userx14/AG-IUP32-8/schematic/HVboard.kicad_sch

## KiCad design schematic/HVboard.kicad_sch (2025-08-31)

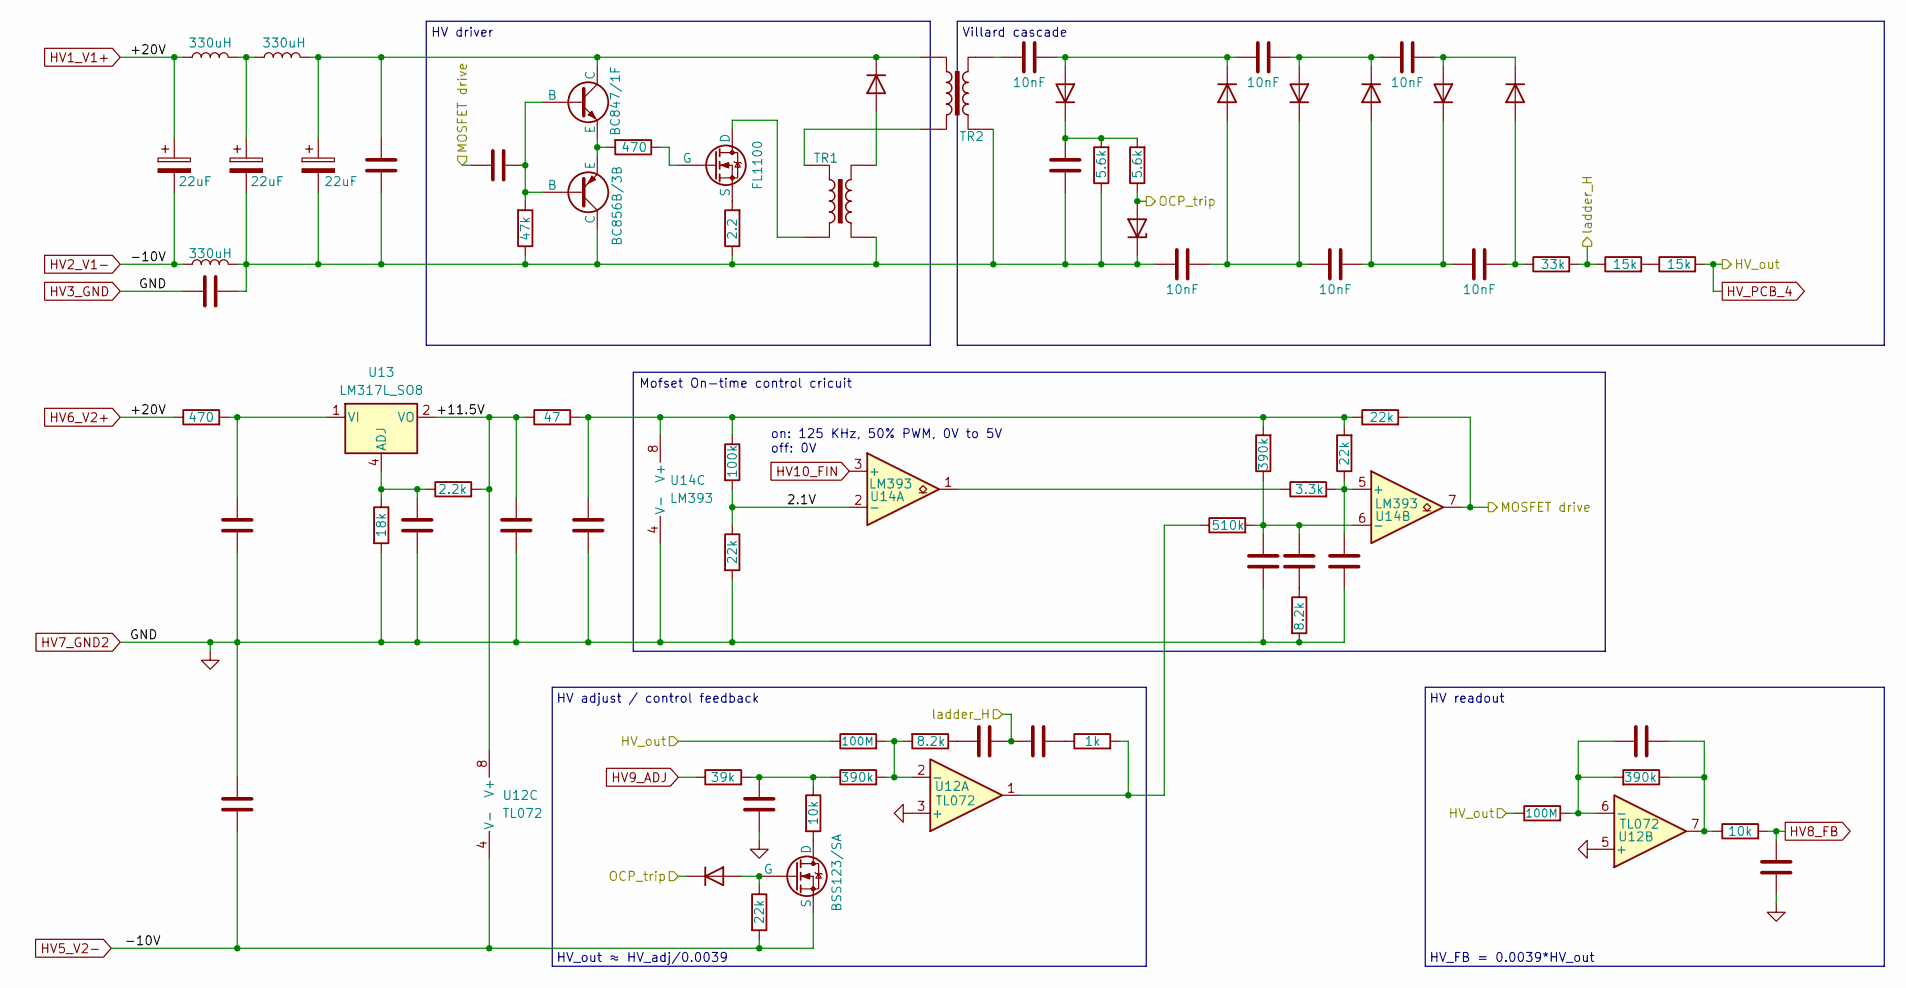
[picture p2: schematic HVboard.kicad_sch]

Parts:
C13, C29, C30, C33, C34, C35, C39: 10nF
C36, C37, C40, C41, C42, C43, C44, C46, C47, C48, C50, C55, C56, C57: C
C38, C53: (no value)
C51, C52, C54: 22uF
D16, D17, D18, D19, D20, D21, D22, D24: D
D25: D_Zener
L5, L6, L7: 330uH
Q1: FL1100
Q10: BSS123/SA
Q14: BC847/1F
Q16: BC856B/3B
R70, R71: 15k
R72: 33k
R73, R85: 8.2k
R74: 1k
R75, R94: 470
R76: 18k
R77: 2.2k
R78: 47
R79, R81, R83, R90: 22k
R80, R88, R98: 390k
R82: 100k
R84: 3.3k
R86: 510k
R87: 39k
R89, R99: 10k
R91, R97: 100M
R92, R96: 5.6k
R93: 2.2
R95: 47k
TR1: TRANSF1
TR2: TRANSF2
U12: TL072
U13: LM317L_SO8; SOIC-8_3.9x4.9mm_P1.27mm
U14: LM393

Connections:
2.1V: R82.2, R83.1, U14.2 (-)
+11.5V: C42.2, R77.2, R78.1, U12.8 (V+), U13.2 (VO), U13.3 (VO), U13.6 (VO), U13.7 (VO)
GND: C38.1, C40.1, C41.1, C42.1, C43.1, C44.1, C47.1, C48.2, C53.1, C57.1, R76.2, R83.2, R85.2, U12.3 (+), U12.5 (+), U14.4 (V-)
HV1_V1+: C54.1, L5.1, R75.1
HV2_V1-: C38.2, C54.2, L6.1, Q10.3 (S), R90.2, U12.4 (V-)
HV8_FB: C57.2, R99.2
HV9_ADJ: R87.1
HV10_FIN: U14.3 (+)
HV_PCB_4: R70.2, R91.1, R97.1
MOSFET drive: C55.2, R79.2, U14.7
unnamed: C13.1, C33.2, D17.1 (K), D18.2 (A)
unnamed: C13.2, D16.2 (A), R72.1
unnamed: C29.1, C30.2, D18.1 (K), D19.2 (A)
unnamed: C29.2, D16.1 (K), D17.2 (A)
unnamed: C30.1, C39.2, D20.1 (K), D22.2 (A)
unnamed: C33.1, C34.2, D19.1 (K), D20.2 (A)
unnamed: C34.1, C35.2, C51.2, C52.2, C53.2, C56.2, D25.1 (K), L6.2, Q16.1 (C), R93.1, R95.1, R96.1, TR1.1, TR2.3
unnamed: C35.1, D22.1 (K), R92.2, R96.2
unnamed: C36.1, R73.1
unnamed: C37.1, R74.1
unnamed: C39.1, TR2.4
unnamed: C40.2, R75.2, U13.1 (VI)
unnamed: C41.2, R76.1, R77.1, U13.4 (ADJ)
unnamed: C43.2, R78.2, R79.1, R80.2, R81.2, R82.1, U14.8 (V+)
unnamed: C44.2, R81.1, R84.2, U14.5 (+)
unnamed: C46.1, R85.1
unnamed: C46.2, C47.2, R80.1, R86.2, U14.6 (-)
unnamed: C48.1, R87.2, R88.1, R89.1
unnamed: C50.1, R97.2, R98.2, U12.6 (-)
unnamed: C50.2, R98.1, R99.1, U12.7
unnamed: C51.1, L5.2, L7.1
unnamed: C52.1, C56.1, D24.1 (K), L7.2, Q14.1 (C), TR2.1
unnamed: C55.1, Q14.2 (B), Q16.2 (B), R95.2
unnamed: D21.2 (A), Q10.2 (G), R90.1
unnamed: D24.2 (A), TR1.2
unnamed: Q1.1 (D), TR1.4
unnamed: Q1.2 (G), R94.1
unnamed: Q1.3 (S), R93.2
unnamed: Q10.1 (D), R89.2
unnamed: Q14.3 (E), Q16.3 (E), R94.2
unnamed: R70.1, R71.2
unnamed: R73.2, R88.2, R91.2, U12.2 (-)
unnamed: R74.2, R86.1, U12.1
unnamed: R84.1, U14.1
unnamed: TR1.3, TR2.2
OCP_trip: D21.1 (K), D25.2 (A), R92.1
ladder_H: C36.2, C37.2, R71.1, R72.2

Notes on the sheet:
HV_FB = 0.0039*HV_out
HV readout
Villard cascade
on: 125 KHz, 50% PWM, 0V to 5V off: 0V
HV driver
HV_out ≈ HV_adj/0.0039
Mofset On-time control cricuit
HV adjust / control feedback
