userx14/AG-IUP32-8/schematic/schematic.kicad_sch

## KiCad design schematic/schematic.kicad_sch (2025-08-31)

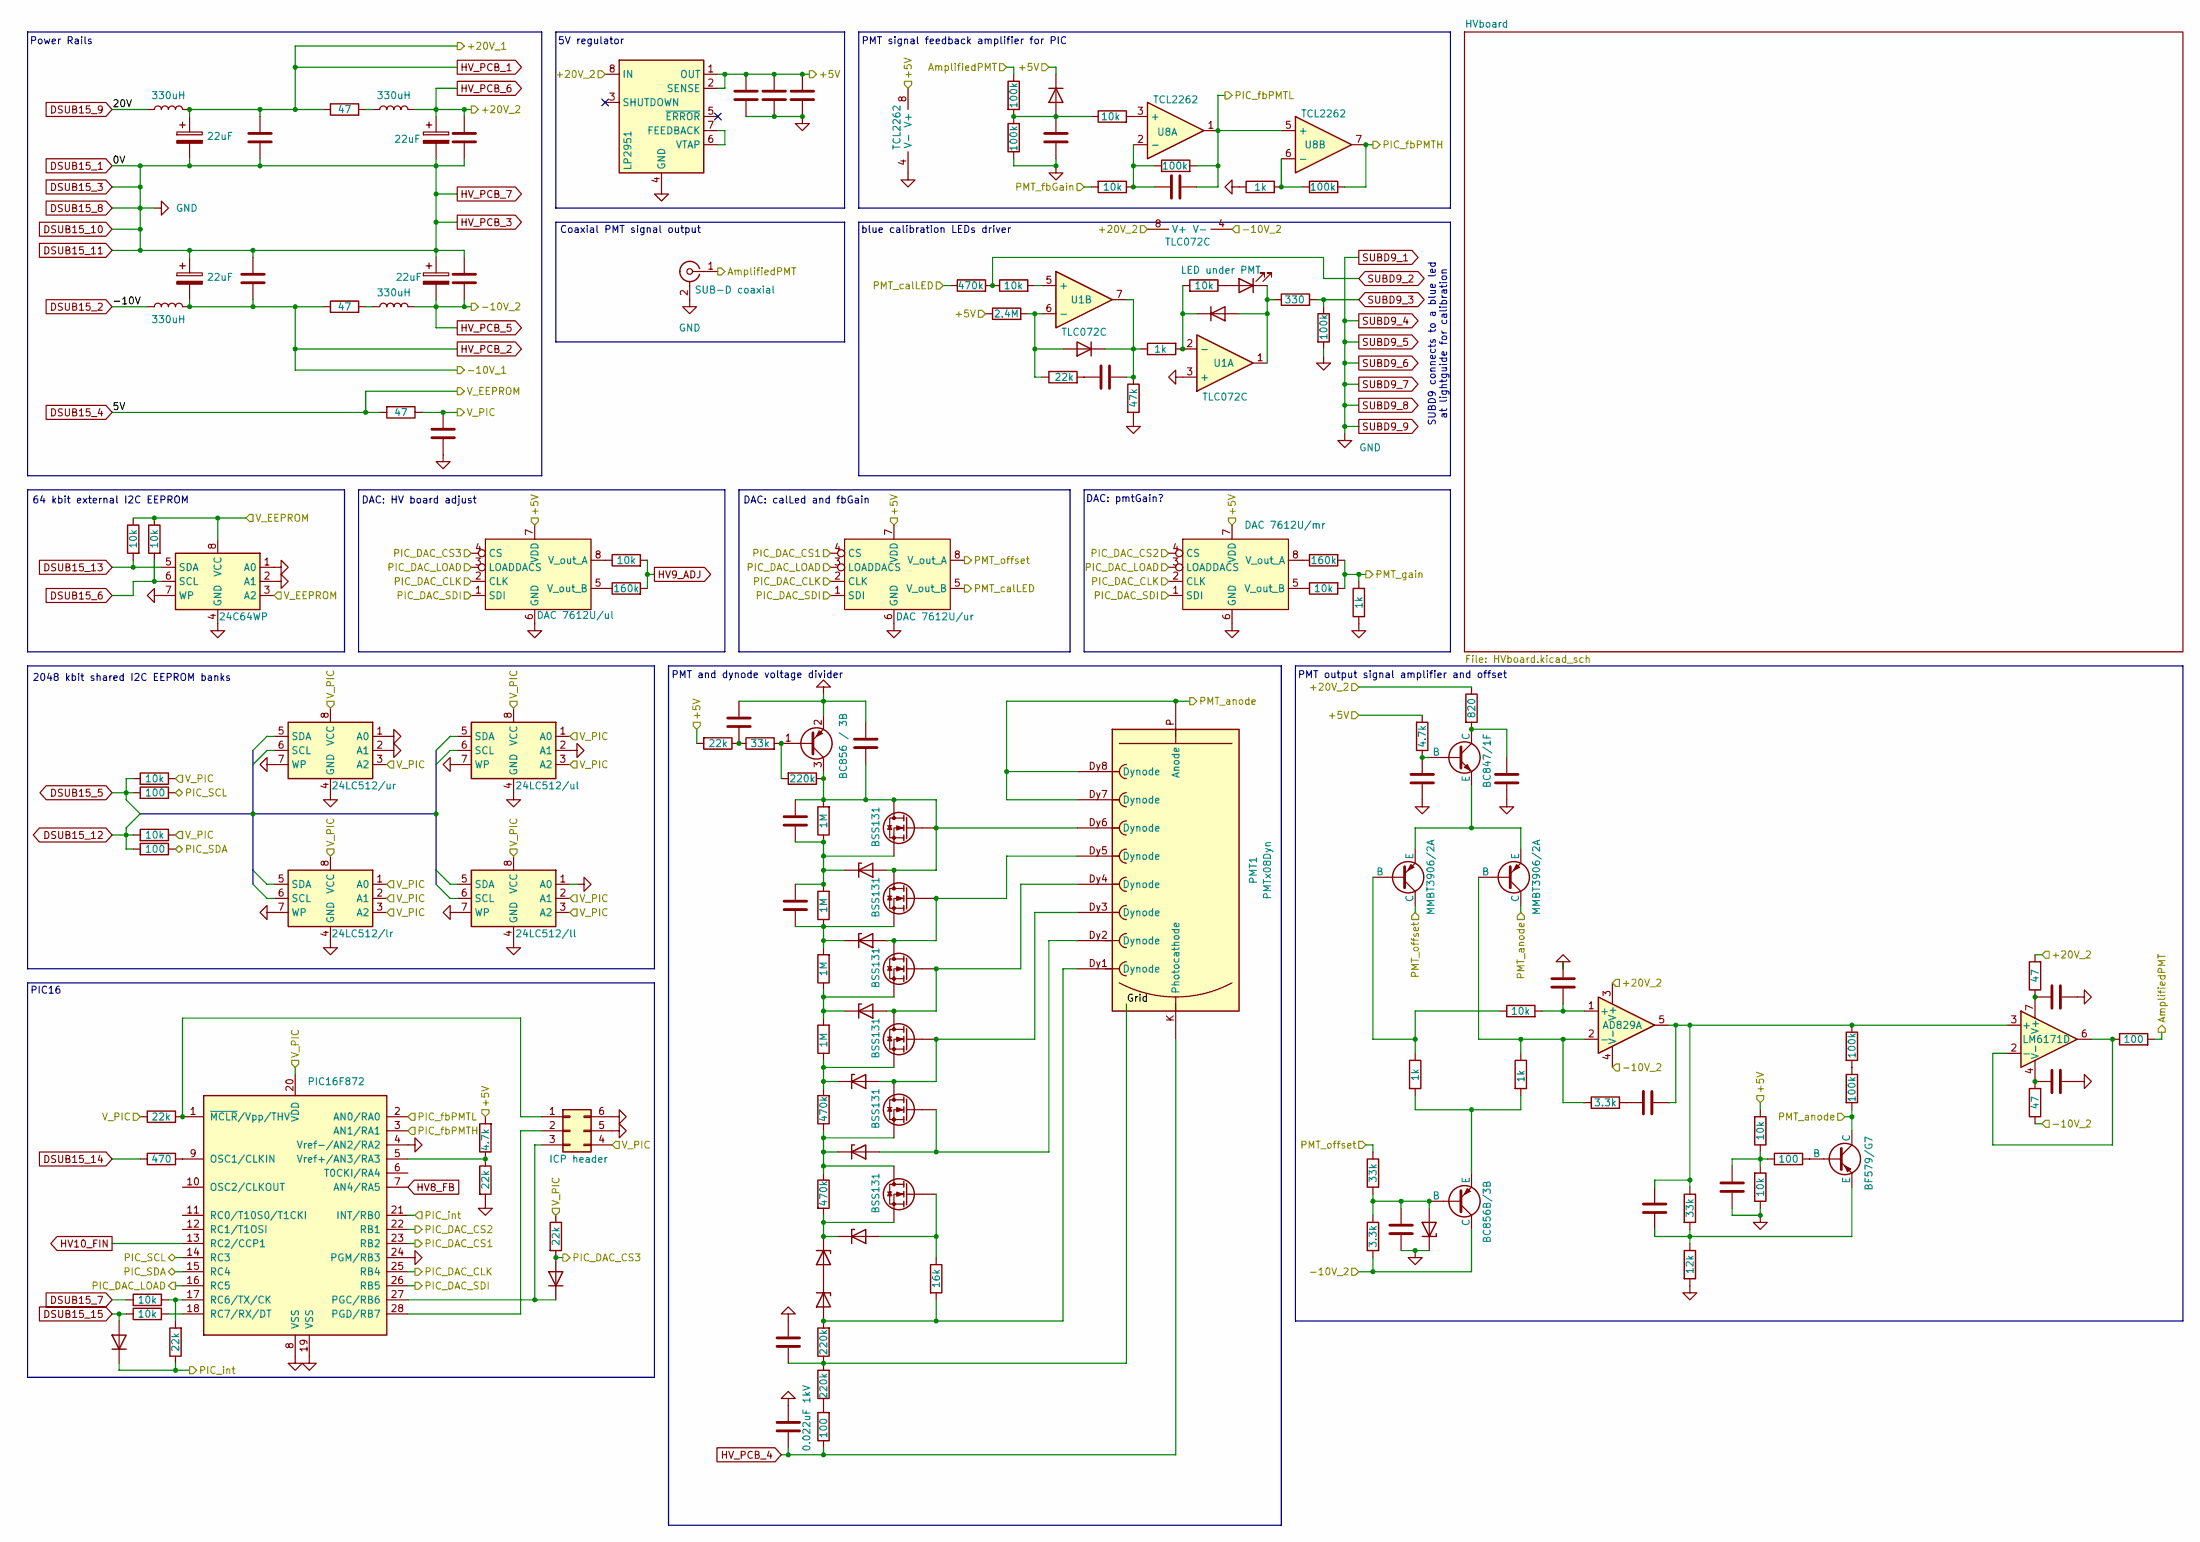
[picture p3: schematic schematic.kicad_sch]

Parts:
C1, C2, C5, C6, C9, C11, C12, C14, C15, C16, C17, C18, C20, C21, C22, C23, C24, C25, C26, C27, C28, C31, C32, C45: C
C3, C4, C7, C8: 22uF
C10: 0.022uF 1kV
C19: 0.022uF 1000V
D1, D2, D4, D5, D6, D7, D8, D9, D15: D_Zener
D3, D10, D11, D13, D14: D
D12: LED under PMT
IC1: DAC 7612U/mr
IC2: DAC 7612U/ul
IC3: DAC 7612U/ur
J1: SUB-D coaxial
J2: ICP header
L1, L2, L3, L4: 330uH
PMT1: PMTx08Dyn
Q2: BF579/G7
Q3, Q4, Q5, Q6, Q9, Q11: BSS131
Q7: BC856 / 3B; SOT-23
Q8: BC847/1F
Q12, Q13: MMBT3906/2A
Q15: BC856B/3B
R1, R7, R9, R48, R52, R54, R56: 100k
R2, R16, R17, R21, R66: 100
R3, R4, R5, R6, R13: 47
R8, R32, R59: 33k
R10: 12k
R11, R14, R15, R18, R19, R35, R42, R46, R49, R51, R53, R62, R63, R64, R65: 10k
R12, R67: 1k; r
R20: 470
R22, R23, R31: 220k
R24: 16k
R25, R26, R43: 470k
R27, R28, R29, R30: 1M
R33, R34, R37, R38, R44, R69: 22k
R36, R50: 160k
R39, R58: 4.7k
R40: 2.4M
R41, R55, R68: 1k
R45: 47k
R47: 330
R57: 820
R60, R61: 3.3k
U1: TLC072C
U2: AD829A
U3: 24C64WP; SOIC-8_3.9x4.9mm_P1.27mm
U4: 24LC512/lr
U5: 24LC512/ur
U6: 24LC512/ll
U7: 24LC512/ul
U8: TCL2262
U9: LP2951; SOIC-8_3.9x4.9mm_P1.27mm
U10: LM6171D; SOIC-8_3.9x4.9mm_P1.27mm
U11: PIC16F872

Connections:
+5V: C12.1, C14.2, C20.2, D13.1 (K), IC1.7 (VDD), IC2.7 (VDD), IC3.7 (VDD), R33.2, R39.2, R40.1, R58.2, R64.2, U8.8 (V+), U9.1 (OUT), U9.2 (SENSE)
AmplifiedPMT: J1.1 (In), R1.1, R2.2
DSUB15_1: C1.2, C2.2, C3.2, C4.1, C5.2, C6.1, C7.2, C8.1, C10.2, C11.1, C12.2, C14.1, C17.1, C18.1, C19.1, C20.1, C23.1, C25.2, C26.1, C27.2, C28.2, C31.2, C32.1, C45.1, D15.1 (K), IC1.6 (GND), IC2.6 (GND), IC3.6 (GND), J1.2 (Ext), J2.5, J2.6, Q7.2 (E), R10.2, R38.2, R45.2, R48.2, R55.1, R56.1, R65.1, R68.1, U1.3 (+), U3.1 (A0), U3.2 (A1), U3.4 (GND), U3.7 (WP), U4.4 (GND), U4.7 (WP), U5.1 (A0), U5.2 (A1), U5.4 (GND), U5.7 (WP), U6.1 (A0), U6.4 (GND), U6.7 (WP), U7.2 (A1), U7.4 (GND), U7.7 (WP), U8.4 (V-), U9.4 (GND), U11.4 (Vref-/AN2/RA2), U11.8 (VSS), U11.19 (VSS), U11.24 (PGM/RB3)
DSUB15_2: L2.1
DSUB15_4: R13.2, R18.1, R19.1, U3.3 (A2), U3.8 (VCC)
DSUB15_5: R14.2, R16.2
DSUB15_6: R19.2, U3.6 (SCL)
DSUB15_7: R62.1
DSUB15_9: L1.1
DSUB15_12: R15.2, R17.2
DSUB15_13: R18.2, U3.5 (SDA)
DSUB15_14: R20.1
DSUB15_15: D14.2 (A), R63.1
Grid: C19.2, R22.2, R23.1
HV8_FB: U11.7 (AN4/RA5)
HV9_ADJ: R35.2, R36.2
HV10_FIN: U11.13 (RC2/CCP1)
HV_PCB_1: C3.1, C5.1, L1.2, R5.1
HV_PCB_2: C4.2, C6.2, L2.2, R6.1
HV_PCB_4: C10.1, PMT1.K (Photocathode), R21.1
HV_PCB_5: C8.2, C25.1, L4.2, Q15.1 (C), R3.1, R61.2, U1.4 (V-), U2.4 (V-)
HV_PCB_6: C7.1, C45.2, L3.2, R4.2, R57.1, U1.8 (V+), U2.3 (V+), U9.8 (IN)
unnamed: C1.1, R3.2, U10.4 (V-)
unnamed: C2.1, R4.1, U10.7 (V+)
unnamed: C9.1, R60.2
unnamed: C15.1, D8.1 (K), Q9.S, R27.2, R29.1
unnamed: C15.2, C16.1, D9.1 (K), Q11.S, R29.2, R30.1
unnamed: C16.2, C17.2, D9.2 (A), PMT1.Dy6 (Dynode), Q7.3 (C), Q9.D, Q11.D, Q11.G, R30.2, R31.1
unnamed: C18.2, R32.1, R33.1
unnamed: C21.1, R44.2
unnamed: C21.2, D11.1 (K), R41.1, R45.1, U1.7
unnamed: C22.1, R51.1, R52.1, U8.2 (-)
unnamed: C23.2, D13.2 (A), R1.2, R53.1, R56.2
unnamed: C9.2, C24.1, R7.1, R8.1, U2.5, U10.3 (+)
unnamed: C24.2, Q2.3 (E), R8.2, R10.1
unnamed: C26.2, R64.1, R65.2, R66.2
unnamed: C27.1, Q8.1 (C), R57.2
unnamed: C28.1, Q8.2 (B), R58.1
unnamed: C31.1, R11.2, U2.1 (+)
unnamed: C32.2, D15.2 (A), Q15.2 (B), R59.2, R61.1
unnamed: D1.1 (K), D6.2 (A)
unnamed: D1.2 (A), PMT1.Dy1 (Dynode), R23.2, R24.2
unnamed: D2.1 (K), D6.1 (K), Q3.S, R25.2
unnamed: D2.2 (A), Q3.G, R24.1
unnamed: D3.1 (K), J2.3, U11.27 (PGC/RB6)
unnamed: D4.1 (K), Q3.D, Q4.S, R25.1, R26.1
unnamed: D4.2 (A), PMT1.Dy2 (Dynode), Q4.G
unnamed: D5.1 (K), Q5.S, R26.2, R28.1
unnamed: D5.2 (A), PMT1.Dy3 (Dynode), Q4.D, Q5.G
unnamed: D7.1 (K), Q6.S, R27.1, R28.2
unnamed: D7.2 (A), PMT1.Dy4 (Dynode), Q5.D, Q6.G
unnamed: D8.2 (A), PMT1.Dy5 (Dynode), Q6.D, Q9.G
unnamed: D10.1 (K), R41.2, R46.2, U1.2 (-)
unnamed: D10.2 (A), D12.1 (K), R47.1, U1.1
unnamed: D11.2 (A), R40.2, R44.1, U1.6 (-)
unnamed: D12.2 (A), R46.1
unnamed: IC1.5 (V_out_B), R49.1
unnamed: IC1.8 (V_out_A), R50.1
unnamed: IC2.5 (V_out_B), R36.1
unnamed: IC2.8 (V_out_A), R35.1
unnamed: J2.1, R37.2, U11.1 (~MCLR/Vpp/THV)
unnamed: J2.2, U11.28 (PGD/RB7)
unnamed: L3.1, R5.2
unnamed: L4.1, R6.2
unnamed: Q2.2 (B), R66.1
unnamed: Q7.1 (B), R31.2, R32.2
unnamed: Q12.2 (B), R11.1, R67.1
unnamed: Q8.3 (E), Q12.3 (E), Q13.3 (E)
unnamed: Q13.2 (B), R12.1, R60.1, U2.2 (-)
unnamed: Q15.3 (E), R12.2, R67.2
unnamed: R2.1, U10.2 (-), U10.6
unnamed: R7.2, R9.1
unnamed: R20.2, U11.9 (OSC1/CLKIN)
unnamed: R21.2, R22.1
unnamed: R38.1, R39.1, U11.5 (Vref+/AN3/RA3)
unnamed: R42.2, U1.5 (+)
unnamed: R53.2, U8.3 (+)
unnamed: R54.1, R55.2, U8.6 (-)
unnamed: R62.2, R69.2, U11.17 (RC6/TX/CK)
unnamed: R63.2, U11.18 (RC7/RX/DT)
unnamed: U9.6 (VTAP), U9.7 (FEEDBACK)
PIC_DAC_CLK: IC1.2 (CLK), IC2.2 (CLK), IC3.2 (CLK), U11.25 (RB4)
PIC_DAC_CS1: IC3.4 (CS), U11.23 (RB2)
PIC_DAC_CS2: IC1.4 (CS), U11.22 (RB1)
PIC_DAC_CS3: D3.2 (A), IC2.4 (CS), R34.2
PIC_DAC_LOAD: IC1.3 (LOADDACS), IC2.3 (LOADDACS), IC3.3 (LOADDACS), U11.16 (RC5)
PIC_DAC_SDI: IC1.1 (SDI), IC2.1 (SDI), IC3.1 (SDI), U11.26 (RB5)
PIC_SCL: R16.1, U11.14 (RC3)
PIC_SDA: R17.1, U11.15 (RC4)
PIC_fbPMTH: R54.2, U8.7, U11.3 (AN1/RA1)
PIC_fbPMTL: C22.2, R52.2, U8.1, U8.5 (+), U11.2 (AN0/RA0)
PIC_int: D14.1 (K), R69.1, U11.21 (INT/RB0)
PMT_anode: PMT1.Dy7 (Dynode), PMT1.Dy8 (Dynode), PMT1.P (Anode), Q2.1 (C), Q13.1 (C), R9.2
PMT_calLED: IC3.5 (V_out_B), R43.1
PMT_fbGain: R51.2
PMT_gain: R49.2, R50.2, R68.2
PMT_offset: IC3.8 (V_out_A), Q12.1 (C), R59.1
SUBD9_2: R42.1, R43.2
SUBD9_3: R47.2, R48.1
V_PIC: C11.2, J2.4, R13.1, R14.1, R15.1, R34.1, R37.1, U4.1 (A0), U4.2 (A1), U4.3 (A2), U4.8 (VCC), U5.3 (A2), U5.8 (VCC), U6.2 (A1), U6.3 (A2), U6.8 (VCC), U7.1 (A0), U7.3 (A2), U7.8 (VCC), U11.20 (VDD)

Notes on the sheet:
SUBD9 connects to a blue led at lightguide for calibration
blue calibration LEDs driver
5V regulator
PMT and dynode voltage divider
PMT output signal amplifier and offset
DAC: calLed and fbGain
Power Rails
PIC16
PMT signal feedback amplifier for PIC
DAC: pmtGain?
Coaxial PMT signal output
64 kbit external I2C EEPROM
DAC: HV board adjust
2048 kbit shared I2C EEPROM banks
